c0pperdragon/BreadBin/bernd/instructions/JSR.asm

; ---- JSR a
    ORG $2000
    FETCH TMP2
    FETCH TMP3
    PUSH PCHI
    PUSH PCLO
    COPY16 PCLO PCHI TMP2 TMP3
    NEXT

; ---- JSR (a,x)
    ORG $FC00
    FETCH TMP2
    FETCH TMP3    
    PUSH PCHI
    PUSH PCLO
    ADD16 TMP2 TMP3 XLO XHI
    LOAD_POSTINC TMP2 TMP3 V0 PCLO
    LOAD TMP2 TMP3 V0 PCHI    
    NEXT
