c0pperdragon/BreadBin/bernd/instructions/TAX.asm

; ---- TAX i
    ORG $AA00
    BRINDEX16 TAX_to16
; to 8
    GET ALO
    SET XLO
    NZ8 XLO
    NEXT
TAX_to16:
    BRACCU16 TAX_16to16
; 8 to 16
    COPY16 XLO XHI ALO V0
    NZ16 XLO XHI
    NEXT
TAX_16to16:
    COPY16 XLO XHI ALO AHI
    NZ16 XLO XHI
    NEXT
    
