c0pperdragon/BreadBin/bernd/instructions/TAY.asm

; ---- TAY i
    ORG $A800
    BRINDEX16 TAY_to16
; to 8
    GET ALO
    SET YLO
    NZ8 YLO
    NEXT
TAY_to16:
    BRACCU16 TAY_16to16
; 8 to 16
    COPY16 YLO YHI ALO V0
    NZ16 YLO YHI
    NEXT
TAY_16to16:
    COPY16 YLO YHI ALO AHI
    NZ16 YLO YHI
    NEXT
