c0pperdragon/BreadBin/bernd/instructions/TXA.asm

; ---- TXA i
    ORG $8A00
    BRACCU16 TXA_to16
; to 8
    GET XLO
    SET ALO
    NZ8 ALO
    NEXT
TXA_to16:
    BRINDEX16 TXA_16to16
; 8 to 16
    COPY16 ALO AHI XLO V0
    NZ16 ALO AHI
    NEXT
TXA_16to16:
    COPY16 ALO AHI XLO XHI 
    NZ16 ALO AHI
    NEXT
